sparkfun/SparkFun_Optical_Tracking_Odometry_Sensor/docs/assets/img/24904-Optical-Tracking-Odometry-Sensor_VReg.jpg

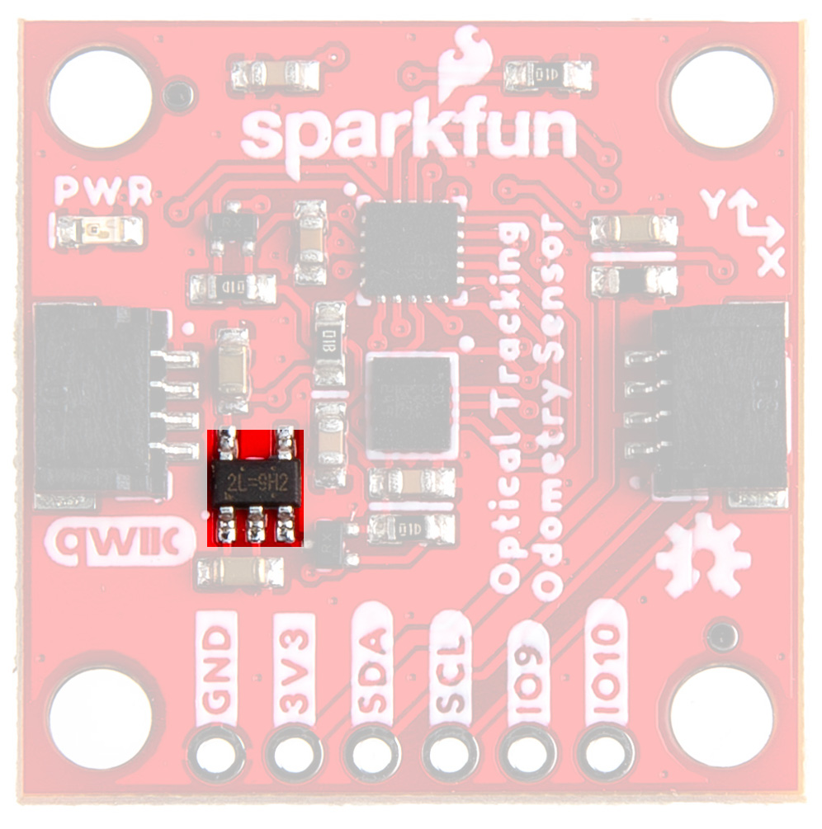
docs/assets/img/24904-Optical-Tracking-Odometry-Sensor_VReg.jpg
