sparkfun/SparkFun_Optical_Tracking_Odometry_Sensor/docs/assets/img/Arduino_Example_7_Output.jpg

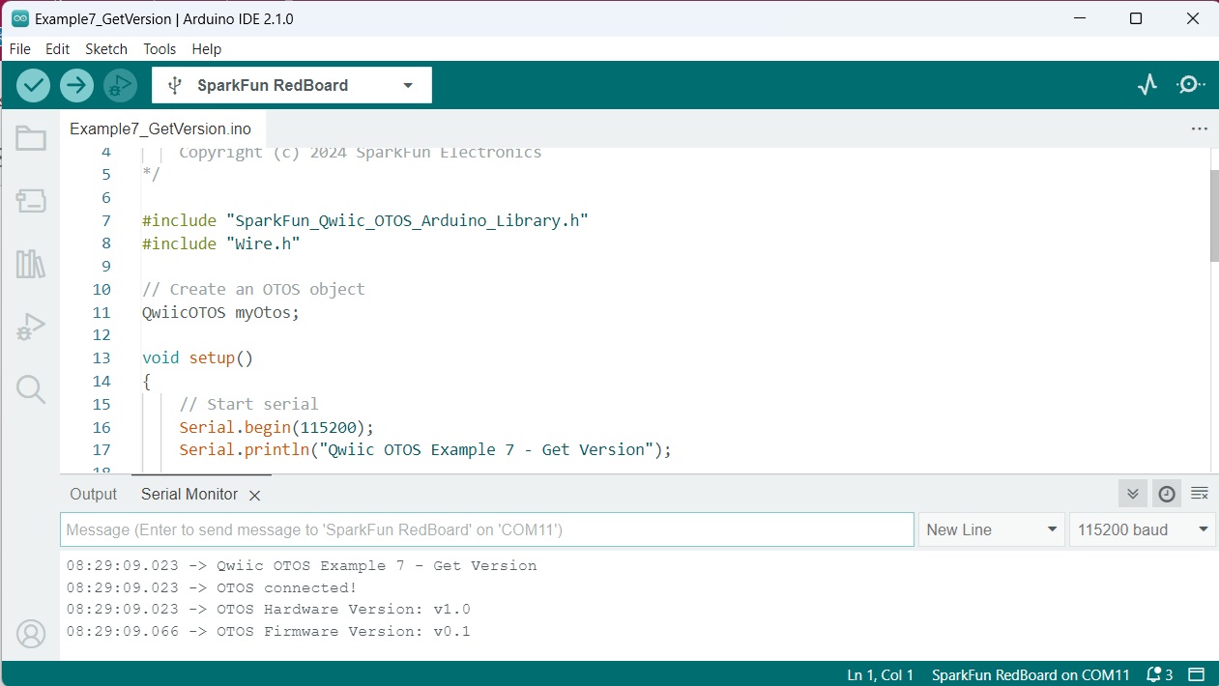
docs/assets/img/Arduino_Example_7_Output.jpg
