sparkfun/SparkFun_Optical_Tracking_Odometry_Sensor/docs/assets/img/SEN-24904-Action-23.jpg

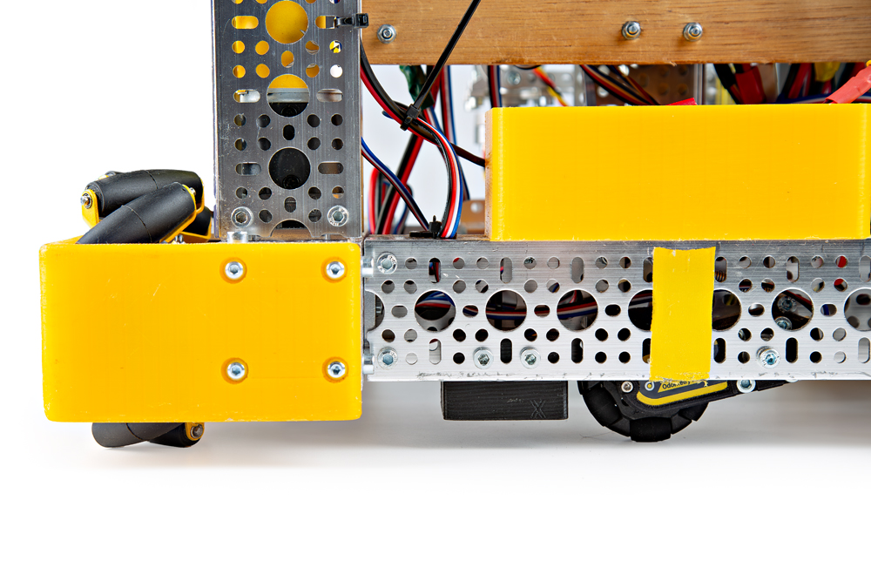
docs/assets/img/SEN-24904-Action-23.jpg
