sparkfun/SparkFun_Optical_Tracking_Odometry_Sensor/docs/assets/img/SEN-24904-Optical-Tracking-Odometry-Sensor-Back-No-Sticker.jpg

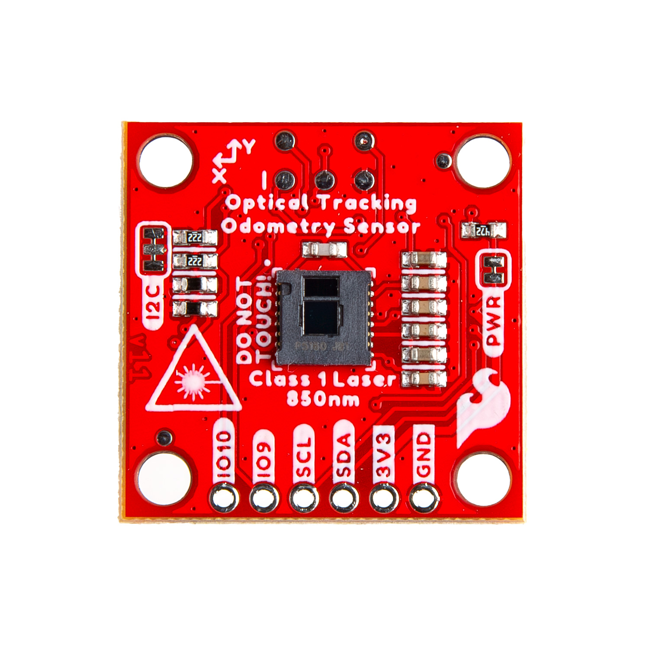
docs/assets/img/SEN-24904-Optical-Tracking-Odometry-Sensor-Back-No-Sticker.jpg
