sparkfun/SparkFun_Optical_Tracking_Odometry_Sensor/Firmware/Lookup_Table_Calibration/Calibration_Data/xcal_6.csv

0.865225 | 0.8758067226890757 | 0.853228813559322 | 0.8556153846153846 | 0.8670689655172413 | 0.8738782608695652 | 0.8739385964912281 | 0.8877079646017699 | 1.010553571428571 | 0.02513513513513514 | 0.002990909090909091 | -0.009614678899082569 | 0.005962962962962963 | 0.004981308411214954 | 0.01061320754716981 | -0.01482857142857143 | -4.807692307692308e-05 | -0.001815533980582524 | -0.01477450980392157 | 0.002237623762376238 | 0.00125 | 0.005050505050505051 | 0.01424489795918367 | 0.003175257731958763 | 0.017 | 0.003947368421052632 | -0.00224468085106383 | -0.003720430107526881 | 0.01389130434782609 | 0.003164835164835165 | -0.002211111111111111 | 0.01266292134831461 | -0.0003863636363636364 | 0.01482758620689655 | -0.0001162790697674419 | 0.02881176470588235 | -0.01227380952380952 | 0.009867469879518071 | -0.01146341463414634 | -0.01275308641975309 | 0.0003875 | -0.03540506329113925 | 0.001384615384615385 | 0.002896103896103896 | 0.003355263157894737 | -0.004106666666666666 | -0.07283783783783783 | 0.003328767123287671 | -0.05086111111111111 | -0.009718309859154929 | -0.01191428571428571 | -0.01921739130434783 | -0.002294117647058824 | -0.05501492537313433 | 0.01503030303030303
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
