sparkfun/SparkFun_Optical_Tracking_Odometry_Sensor/Firmware/SFE/Inc/otosLut.h

/*
    SPDX-License-Identifier: MIT
    
    Copyright (c) 2024 SparkFun Electronics
*/

#pragma once

#include "main.h"

// Resolution variation lookup tables
const uint8_t numLutIndices = 51;
const int8_t lutIndices[numLutIndices] = {-100,-93,-88,-83,-78,-73,-68,-64,-59,-55,-50,-45,-41,-37,-33,-28,-26,-21,-17,-15,-12,-10,-7,-5,-3,0,3,5,7,10,12,15,17,21,26,28,33,37,41,45,50,55,59,64,68,73,78,83,88,93,100};

// In order to minimize flash size, the lookup tables are stored as 2D arrays of
// 8-bit signed integers, which has a resolution of 0.2% per LSB, and is offset
// by 100%. For example, a value of 0 in the lookup table corresponds to a 100%
// scaling factor, and a value of 1 corresponds to 100.2%
const float lutResolution = 0.002f;

const int8_t xResVarLut[numLutIndices][numLutIndices] =
{
    {83,97,101,92,56,52,52,52,45,45,48,45,43,52,36,53,62,19,50,72,52,-5,36,77,114,125,113,62,10,-3,51,72,50,19,60,50,32,51,46,42,48,45,45,48,49,51,49,51,51,55,76},
    {94,93,68,42,42,42,64,46,43,43,39,38,43,39,27,50,62,15,49,68,50,-5,21,81,115,125,105,68,14,7,50,64,48,14,54,46,29,42,40,33,41,44,39,44,44,44,49,45,50,53,53},
    {52,49,51,44,54,51,41,41,43,39,43,34,40,42,29,44,50,12,47,68,43,-2,28,91,122,125,119,50,16,11,53,65,45,14,49,41,28,42,33,36,39,37,42,42,39,41,43,41,43,46,46},
    {67,54,43,46,39,35,39,40,37,39,36,32,34,33,24,41,47,13,42,66,42,-2,34,80,122,125,111,53,27,-7,42,65,41,16,42,42,29,34,37,34,34,36,35,40,40,38,42,40,42,50,49},
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
    {
        // Input values are out of bounds
        return false;
    }

    // Binary search to find the correct x index
    uint8_t low = 0;
    uint8_t high = numLutIndices - 1;
    uint8_t i = 0;
    while (low <= high)
    {
        // New midpoint
        i = (low + high) / 2;

        // Check if we're low or high
        if (lutIndices[i] < inXInt)
            low = i + 1;
        else if (lutIndices[i] > inXInt)
            high = i - 1;
        else
            break;
    }

    // Binary search to find the correct y index
    low = 0;
    high = numLutIndices - 1;
    uint8_t j = 0;
    while (low <= high)
    {
        // New midpoint
        j = (low + high) / 2;

        // Check if we're low or high
        if (lutIndices[j] < inYInt)
            low = j + 1;
        else if (lutIndices[j] > inYInt)
            high = j - 1;
        else
            break;
    }

    // Get the coordinates of the four corners of the square around the input
    float x1 = lutIndices[i];
    float y1 = lutIndices[j];
    float x2 = lutIndices[i + 1];
    float y2 = lutIndices[j + 1];

    // Pre-compute the denominator inverse for the bilinear interpolation
    float denomInv = 1.0f / ((x2 - x1) * (y2 - y1));

    // Pre-compute the difference between the input and bounds
    float dx1 = inX - x1;
    float dy1 = inY - y1;
    float dx2 = x2 - inX;
    float dy2 = y2 - inY;

    // Pre-compute the product of the differences
    float dx1dy1 = dx1 * dy1;
    float dx2dy1 = dx2 * dy1;
    float dx1dy2 = dx1 * dy2;
    float dx2dy2 = dx2 * dy2;

    // Get the values of the four corners of the square around the input for the
    // x lookup table
    float q11 = xResVarLut[j][i];
    float q12 = xResVarLut[j][i + 1];
    float q21 = xResVarLut[j + 1][i];
    float q22 = xResVarLut[j + 1][i + 1];

    // Bilinear interpolation for the x lookup table
    outX = (q11 * dx2dy2 + q21 * dx1dy2 + q12 * dx2dy1 + q22 * dx1dy1) * denomInv;

    // Get the values of the four corners of the square around the input for the
    // y lookup table
    q11 = yResVarLut[j][i];
    q12 = yResVarLut[j][i + 1];
    q21 = yResVarLut[j + 1][i];
    q22 = yResVarLut[j + 1][i + 1];

    // Bilinear interpolation for the y lookup table
    outY = (q11 * dx2dy2 + q21 * dx1dy2 + q12 * dx2dy1 + q22 * dx1dy1) * denomInv;

    // Adjust scale of outputs
    outX = (outX * lutResolution) + 1.0f;
    outY = (outY * lutResolution) + 1.0f;

    // Done!
    return true;
}
